unsurv/OpenCartoCam/docs/_static/3D_preview_front.PNG

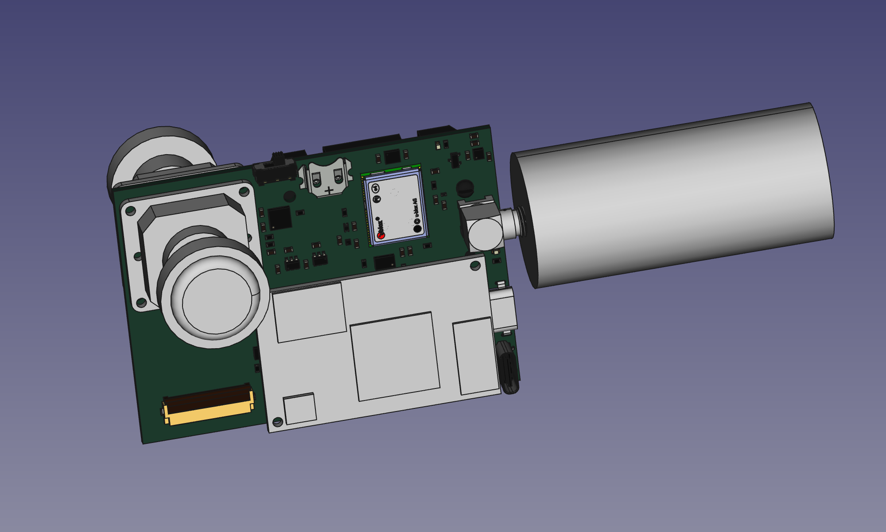
docs/_static/3D_preview_front.PNG
