unsurv/OpenCartoCam/docs/_static/PCB_view.PNG

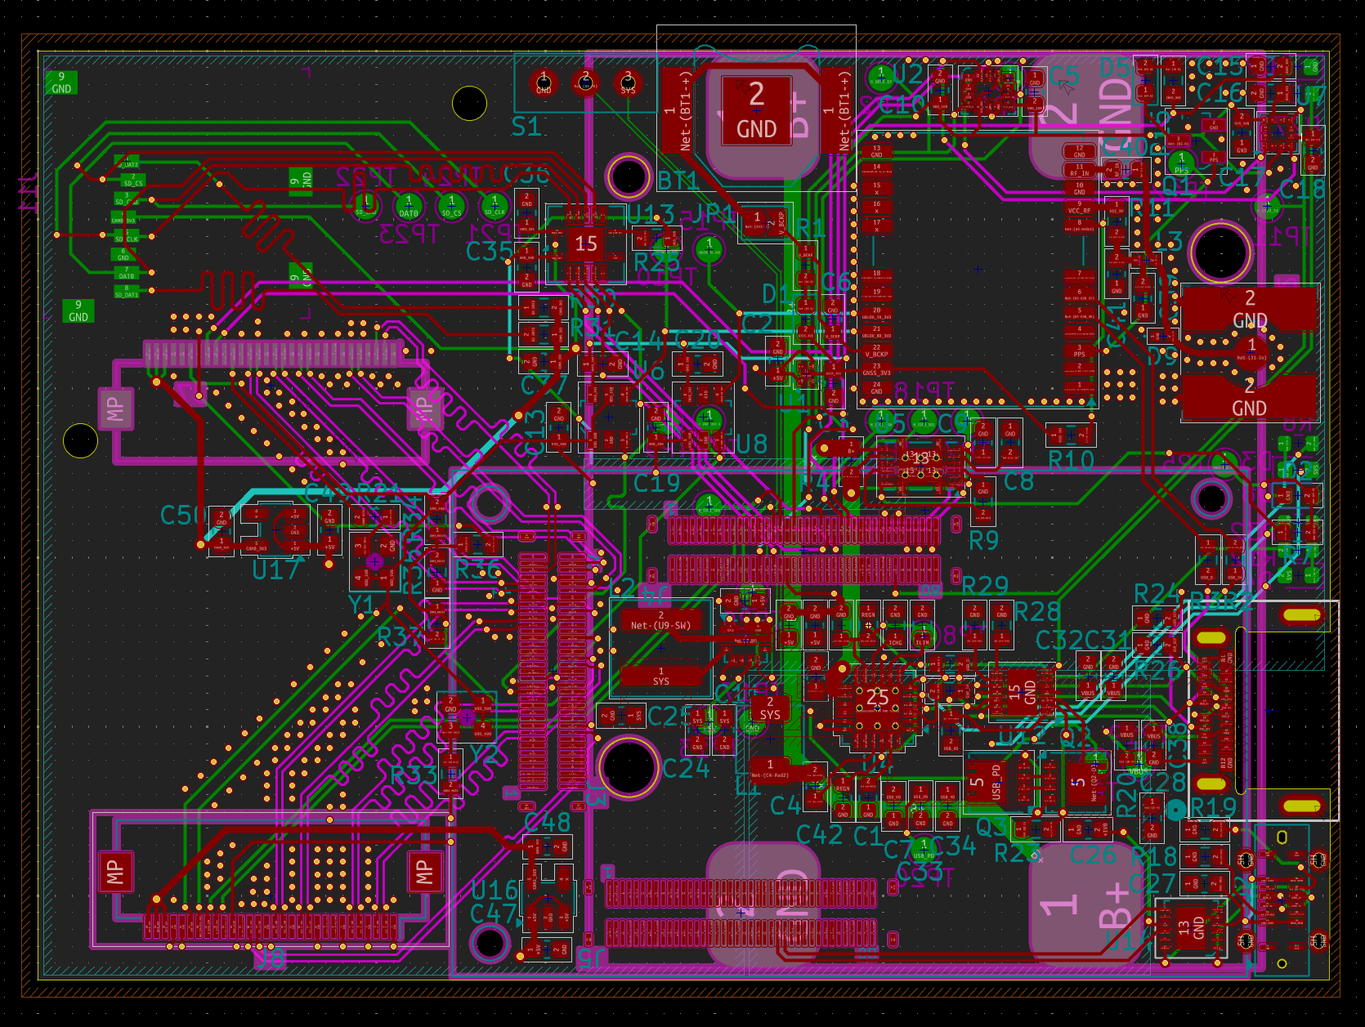
docs/_static/PCB_view.PNG
